korginc/nts-1-customizations/Custom_Panel_RevC/Arduino/examples/Blank_Template/Blank_Template.ino

/* 
    Blank Template for NTS-1 Custom Panel reference board rev.B
    
    This is free and unencumbered software released into the public domain.
    
    Anyone is free to copy, modify, publish, use, compile, sell, or
    distribute this software, either in source code form or as a compiled
    binary, for any purpose, commercial or non-commercial, and by any
    means.
    
    In jurisdictions that recognize copyright laws, the author or authors
    of this software dedicate any and all copyright interest in the
    software to the public domain. We make this dedication for the benefit
    of the public at large and to the detriment of our heirs and
    successors. We intend this dedication to be an overt act of
    relinquishment in perpetuity of all present and future rights to this
    software under copyright law.
    
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
    For more information, please refer to <http://unlicense.org/>
//*/

// --- NTS-1 main board interface ------------------------------------------------------------------
#include <nts1.h>

NTS1 nts1;

// --- Arduino Sketch Entry ------------------------------------------------------------------------

void setup() {
  nts1.init();
  
  // put your setup code here, to run once:

}

// --- Arduino Sketch Idle Loop ----------------------------------------------------------------------

void loop() {
  nts1.idle();

  // put your main code here, to run repeatedly:

}
